kumarveluru/12-Lead-Holter-Monitor/3D Models Imported/TPS63001DRCR.step

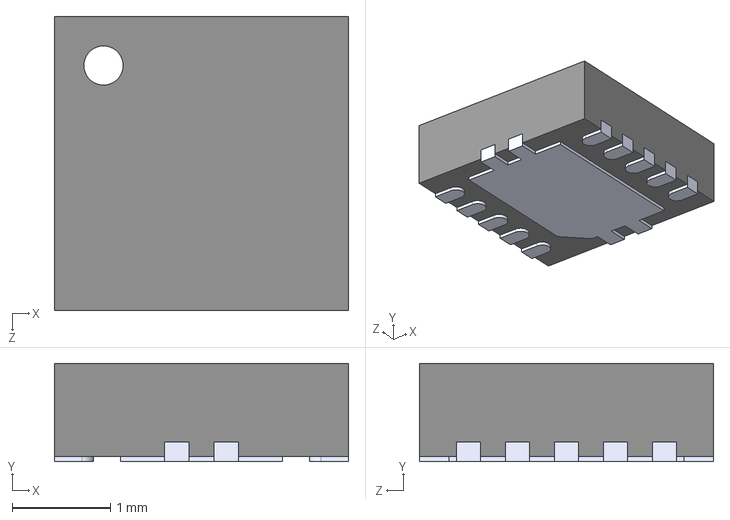
[picture p20: CAD file, 2026-05-06]
3D Models Imported/TPS63001DRCR.step
3.00 x 1.00 x 3.00 mm
