kumarveluru/12-Lead-Holter-Monitor/3D Models Imported/MCP73831T-2ACI_OT.step

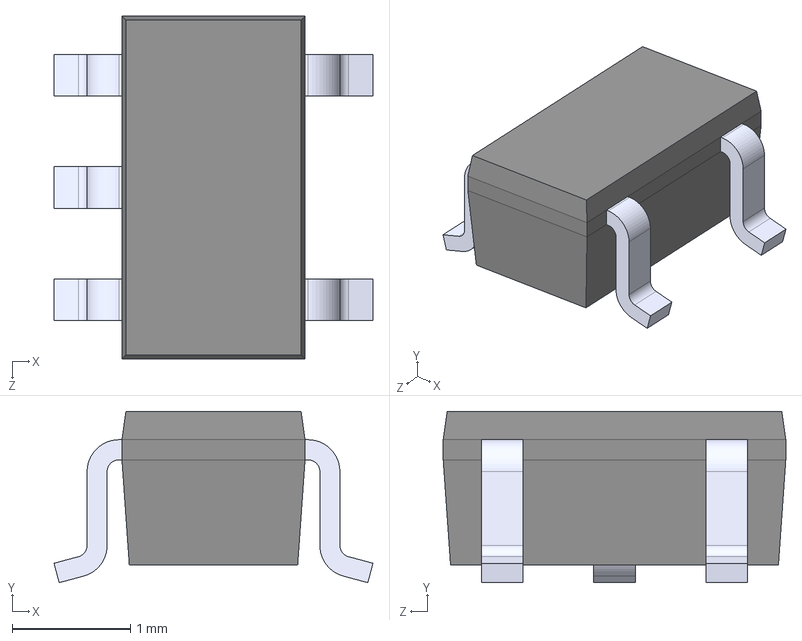
[picture p21: CAD file, 2026-05-06]
3D Models Imported/MCP73831T-2ACI_OT.step
2.70 x 1.45 x 2.90 mm
